hilderonny/stromzaehler-pi/images/0994923.png

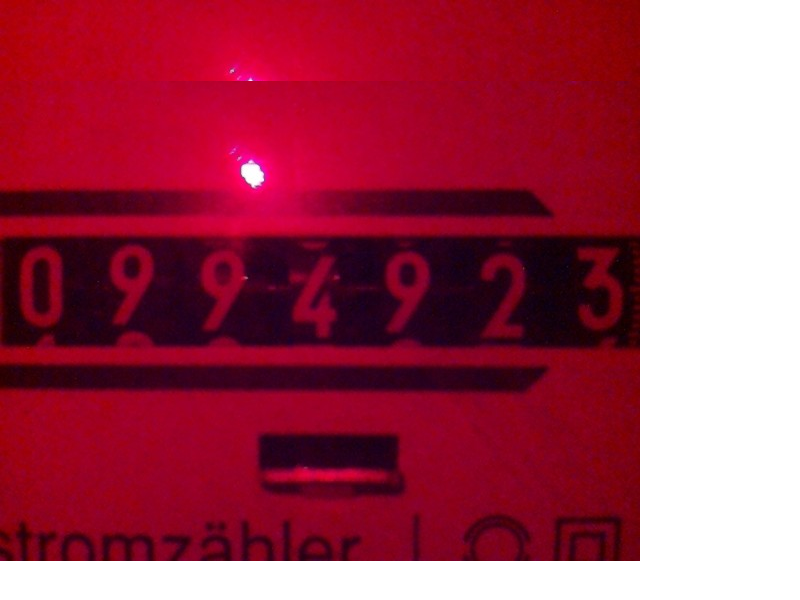
images/0994923.png
